willthree123/WF50/wf50/IMG_20210526_002848_072.jpg

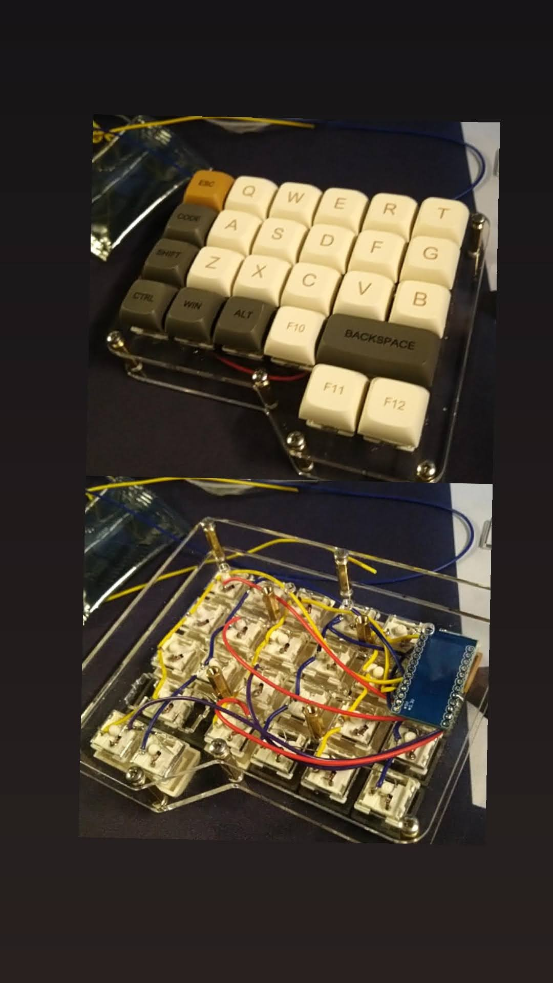
wf50/IMG_20210526_002848_072.jpg
