willthree123/WF50/wf50/IMG_20210527_215114_507.jpg

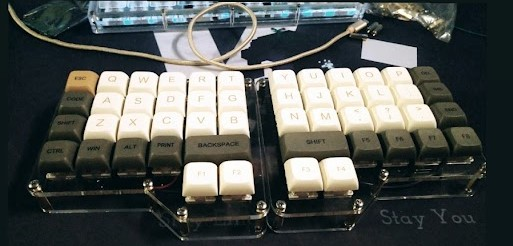
wf50/IMG_20210527_215114_507.jpg
